MalteP/espweather/pictures/v1_revd_btm.png

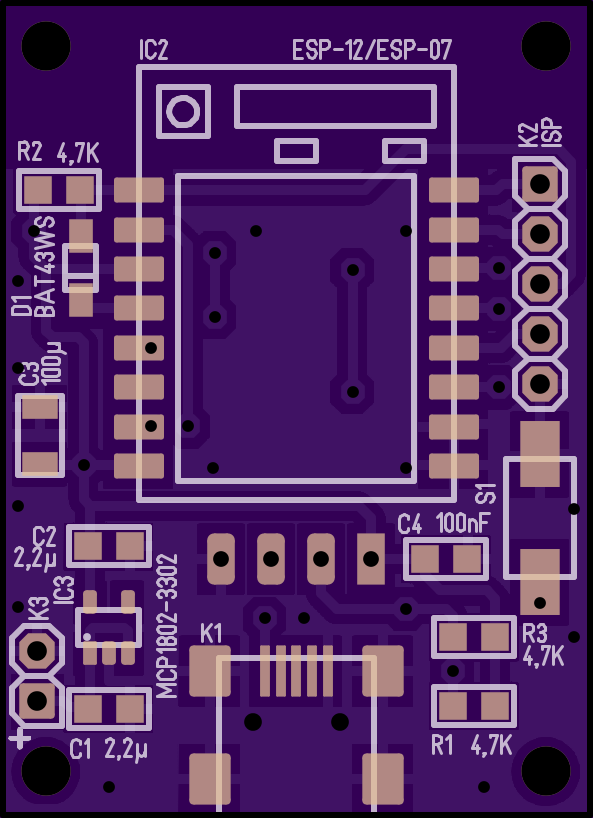
pictures/v1_revd_btm.png
