MalteP/espweather/pictures/v1_revd_top.png

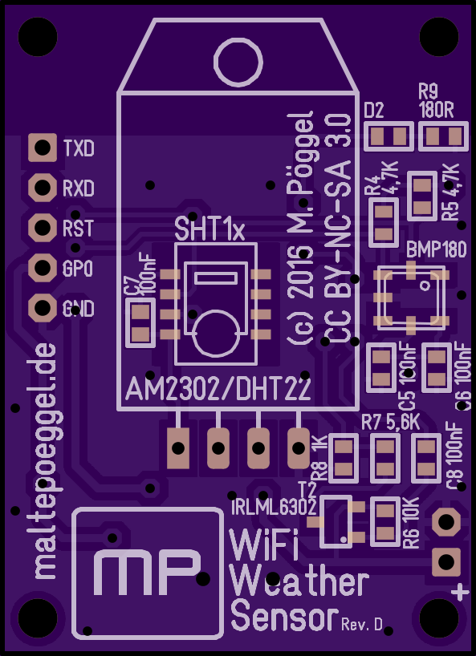
pictures/v1_revd_top.png
