MalteP/espweather/firmware/user/user_main.c

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
#include <esp8266.h>
#include "httpd.h"
#include "config.h"
#include "httpdespfs.h"
#include "cgisensor.h"
#include "cgibuild.h"
#include "cgiwifi.h"
#include "cgiconfig.h"
#include "stdout.h"
#include "auth.h"
#include "espfs.h"
#include "battery.h"
#include "sensors.h"
#include "push.h"

void init_done(void);


// Password authentication for admin interface
int myPassFn(HttpdConnData *connData, int no, char *user, int userLen, char *pass, int passLen)
 {
  if(no==0)
   {
    os_strncpy(user, configGet()->admin_user, userLen);
    os_strncpy(pass, configGet()->admin_pass, passLen);
    return 1;
   }
  return 0;
 }


// URLs for esphttpd
HttpdBuiltInUrl builtInUrls[]=
 {
  {"/", cgiRedirect, "/index.html"},
  {"/sensors.cgi", cgiSensor, NULL},
  {"/admin*", authBasic, myPassFn},
  {"/admin/", cgiRedirect, "/admin/index.html"},
  {"/admin/buildinfo.cgi", cgiBuildInfo, NULL},
  {"/admin/wifiscan.cgi", cgiWiFiScan, NULL},
  {"/admin/wifisettings.cgi", cgiWiFiSettings, NULL},
  {"/admin/sensorconfig.cgi", cgiSensorConfig, NULL},
  {"/admin/userconfig.cgi", cgiUserConfig, NULL},
  {"*", cgiEspFsHook, NULL}, //Catch-all cgi function for the filesystem
  {NULL, NULL, NULL}
 };


// Main routine, initialize some basic stuff
void ICACHE_FLASH_ATTR user_init(void)
 {
  // Init some stuff
  stdoutInit();
  batteryInit();
  configInit();
  configLoad();

  // Check if wifi mode is correct
  configCheckWifiMode();

  // Measure battery voltage
  batteryMeasureVoltage();
  if(!batteryCheckVoltage())
   {
    // Voltage too low, go to sleep mode!
    sleepmode();
   }

  // 0x40200000 is the base address for spi flash memory mapping, ESPFS_POS is the position
  // where image is written in flash that is defined in Makefile.
  espFsInit((void*)(0x40200000 + ESPFS_POS));
  httpdInit(builtInUrls, 80);

  // Register callback
  system_init_done_cb(init_done);

  os_printf("Ready\n");
 }


// Initialize wifi, sensors and push data
void ICACHE_FLASH_ATTR init_done(void)
 {
  // Init SoftAP and IP configuration
  configInitSoftAP();
  configInitIP();
  configInitReconnectPolicy();

  // Init sensors
  sensorsInit();

  if(configGet()->sensor_mode==MODE_NORMAL)
   {
    // Normal mode
    pushSensorData();
   } else {
    // Configuration mode
    statusLed(LED_BLINK);
   }
 }
