MalteP/espweather/firmware/user/i2c-common.c

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
#include <esp8266.h>
#include "i2c-common.h"


void ICACHE_FLASH_ATTR i2cInit( void )
 {
  // Disable GPIO interrupts
  ETS_INTR_LOCK();

  // Set pin function to GPIO
  PIN_FUNC_SELECT(I2C_SDA_MUX, I2C_SDA_FUNC);
  PIN_FUNC_SELECT(I2C_SCL_MUX, I2C_SCL_FUNC);

  // Data as open drain
  GPIO_REG_WRITE(GPIO_PIN_ADDR(GPIO_ID_PIN(I2C_SDA_PIN)), GPIO_REG_READ(GPIO_PIN_ADDR(GPIO_ID_PIN(I2C_SDA_PIN))) | GPIO_PIN_PAD_DRIVER_SET(GPIO_PAD_DRIVER_ENABLE));
  GPIO_REG_WRITE(GPIO_ENABLE_ADDRESS, GPIO_REG_READ(GPIO_ENABLE_ADDRESS) | (1 << I2C_SDA_PIN));

  // Clock as open drain
  GPIO_REG_WRITE(GPIO_PIN_ADDR(GPIO_ID_PIN(I2C_SCL_PIN)), GPIO_REG_READ(GPIO_PIN_ADDR(GPIO_ID_PIN(I2C_SCL_PIN))) | GPIO_PIN_PAD_DRIVER_SET(GPIO_PAD_DRIVER_ENABLE));
  GPIO_REG_WRITE(GPIO_ENABLE_ADDRESS, GPIO_REG_READ(GPIO_ENABLE_ADDRESS) | (1 << I2C_SCL_PIN));

  // Enable GPIO interrupts again
  ETS_INTR_UNLOCK();

  // Set ports
  I2C_SDA_HIGH();
  I2C_SCK_HIGH();
 }

// Write command to device
int ICACHE_FLASH_ATTR i2cWriteCmd( uint8_t device, uint8_t value, uint8_t sendstop )
 {
  i2cSendStart();
  // Write address
  if(i2cWriteByte(device<<1))
   {
    i2cSendStop();
    return -1;
   }
  // Write value
  if(i2cWriteByte(value))
   {
    i2cSendStop();
    return -1;
   }
  if(sendstop!=I2C_NO_STOP) i2cSendStop();
  return 0;
 }


// Write 8bit register via i2c
int ICACHE_FLASH_ATTR i2cWriteRegister8( uint8_t device, uint8_t addr, uint8_t value )
 {
  if(i2cWriteCmd(device, addr, I2C_NO_STOP)!=0)
   {
    return -1;
   }
  // Write value
  if(i2cWriteByte(value))
   {
    i2cSendStop();
    return -1;
   }
  i2cSendStop();
  return 0;
 }


// Read 8bit register via i2c
uint8_t ICACHE_FLASH_ATTR i2cReadRegister8( uint8_t device, uint8_t value )
 {
  uint8_t data;
  if(i2cWriteCmd(device, value, I2C_NO_STOP)!=0)
   {
    return 0;
   }
  // Repeated start
  i2cSendStart();
  // Sensor read address
  if(i2cWriteByte((device<<1)|1))
   {
    i2cSendStop();
    return 0;
   }
  // Read and return data
  data = i2cReadByte(0);
  i2cSendStop();
  return data;
 }


// Read 16bit register via i2c
uint16_t ICACHE_FLASH_ATTR i2cReadRegister16( uint8_t device, uint8_t value )
 {
  uint16_t data;
  if(i2cWriteCmd(device, value, I2C_NO_STOP)!=0)
   {
    return 0;
   }
  // Repeated start
  i2cSendStart();
  // Sensor read address
  if(i2cWriteByte((device<<1)|1))
   {
    i2cSendStop();
    return 0;
   }
  // Read and return data
  data = i2cReadByte(1);
  data <<= 8;
  data |= i2cReadByte(0);
  i2cSendStop();
  return data;
 }


// Read 16bit register via i2c (Little endian)
uint16_t ICACHE_FLASH_ATTR i2cReadRegister16LE( uint8_t device, uint8_t value )
 {
  uint16_t data = i2cReadRegister16(device, value);
  return (data >> 8) | (data << 8);
 }


// Read 24bit register via i2c
uint32_t ICACHE_FLASH_ATTR i2cReadRegister24( uint8_t device, uint8_t value )
 {
  uint32_t data;
  if(i2cWriteCmd(device, value, I2C_NO_STOP)!=0)
   {
    return 0;
   }
  // Repeated start
  i2cSendStart();
  // Sensor read address
  if(i2cWriteByte((device<<1)|1))
   {
    i2cSendStop();
    return 0;
   }
  // Read and return data
  data = i2cReadByte(1);
  data <<= 8;
  data |= i2cReadByte(1);
  data <<= 8;
  data |= i2cReadByte(0);
  i2cSendStop();
  return data;
 }

// Send I2C start condition
int ICACHE_FLASH_ATTR i2cSendStart( void )
 {
  I2C_SCK_HIGH();
  I2C_SDA_HIGH();
  i2cDelay();
  I2C_SDA_LOW();
  i2cDelay();
  I2C_SCK_LOW();
  i2cDelay();
 }

// Send I2C stop condition
int ICACHE_FLASH_ATTR i2cSendStop( void )
 {
  I2C_SDA_LOW();
  i2cDelay();
  I2C_SCK_HIGH();
  i2cDelay();
  I2C_SDA_HIGH();
  i2cDelay();
 }

// Write byte to slave
int ICACHE_FLASH_ATTR i2cWriteByte( int byte )
 {
  uint8 bit;
  // Write data
  for(bit=0;bit<8;bit++)
   {
    if(byte&0x80)
     {
      I2C_SDA_HIGH();
     } else {
      I2C_SDA_LOW();
     }
    i2cDelay();
    I2C_SCK_HIGH();
    i2cDelay();
    I2C_SCK_LOW();
    i2cDelay();
    byte <<= 1;
   }
  // Read ACK from slave
  I2C_SDA_HIGH();
  i2cDelay();
  I2C_SCK_HIGH();
  i2cDelay();
  bit = I2C_SDA_READ();
  I2C_SCK_LOW();
  i2cDelay();
  return bit;
 }

// Read byte from slave
int ICACHE_FLASH_ATTR i2cReadByte( int ack )
 {
  uint8 byte = 0;
  uint8 bit;
  // Read data
  for(bit=0;bit<8;bit++)
   {
    I2C_SDA_HIGH();
    i2cDelay();
    I2C_SCK_HIGH();
    i2cDelay();
    byte <<= 1;
    byte |= I2C_SDA_READ();
    I2C_SCK_LOW();
    i2cDelay();
   }
  // Send ACK/NACK to slave
  if(ack)
   {
    I2C_SDA_LOW();
   } else {
    I2C_SDA_HIGH();
   }
  i2cDelay();
  I2C_SCK_HIGH();
  i2cDelay();
  I2C_SCK_LOW();
  i2cDelay();
  return byte;
 }

// Delay between pulses
void ICACHE_FLASH_ATTR i2cDelay( void )
 {
  os_delay_us(I2C_DELAY_US);
 }
