MalteP/espweather/firmware/include/esp8266.h

// Combined include file for esp8266

#include <ctype.h>
#include <stdio.h>
#include <stdlib.h>
#include <string.h>

#include <c_types.h>
#include <ip_addr.h>
#include <espconn.h>
#include <ets_sys.h>
#include <gpio.h>
#include <mem.h>
#include <osapi.h>
#include <user_interface.h>

#include "uart_hw.h"
